McLaren12345/EFIS/Images/IMG_1576.JPG

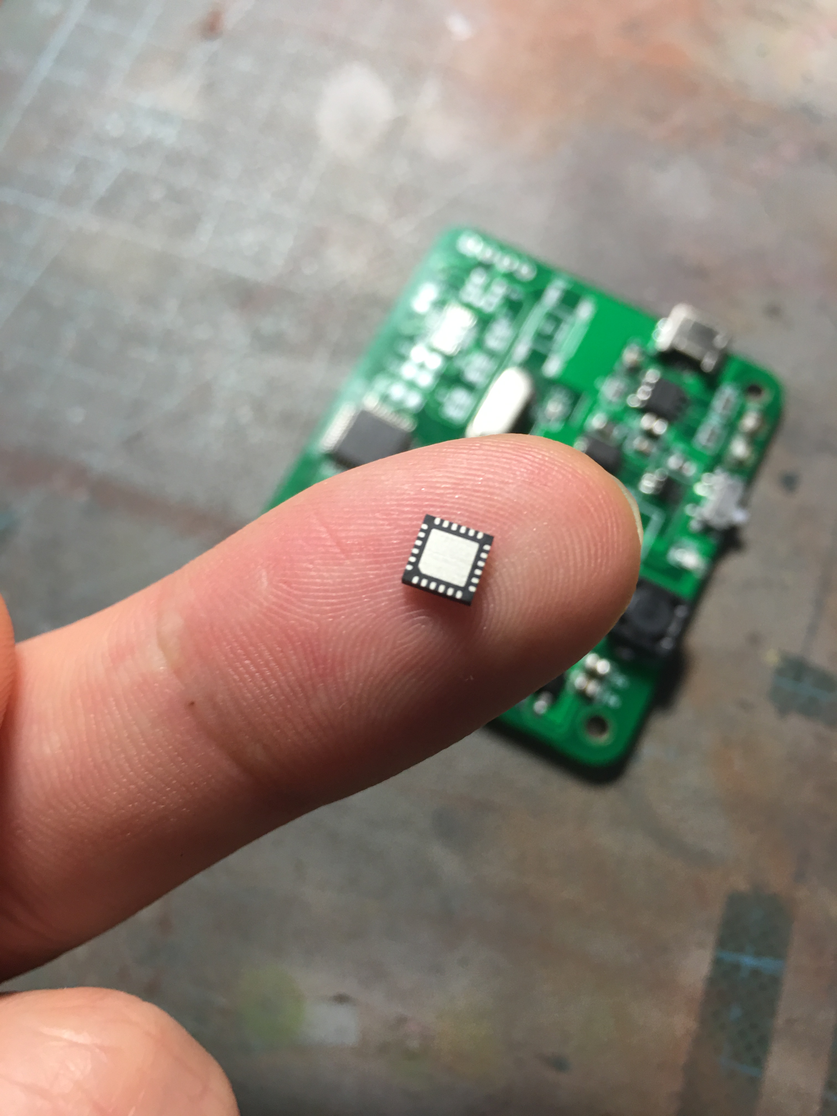
Images/IMG_1576.JPG
