McLaren12345/EFIS/Images/IMG_1605.JPG

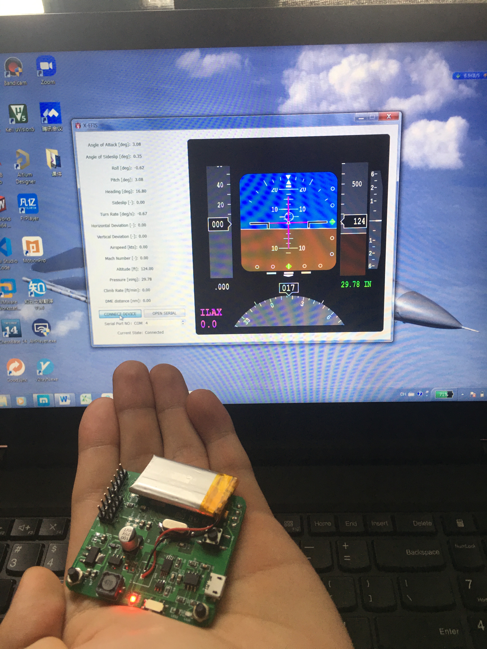
Images/IMG_1605.JPG
