McLaren12345/EFIS/Images/IMG_1611.JPG

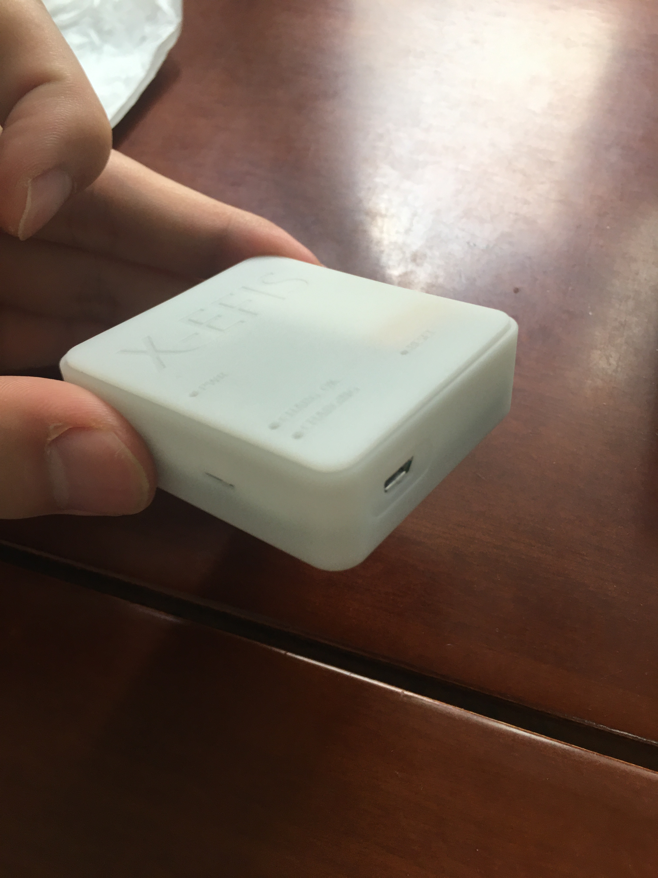
Images/IMG_1611.JPG
