McLaren12345/EFIS/Images/IMG_1615.JPG

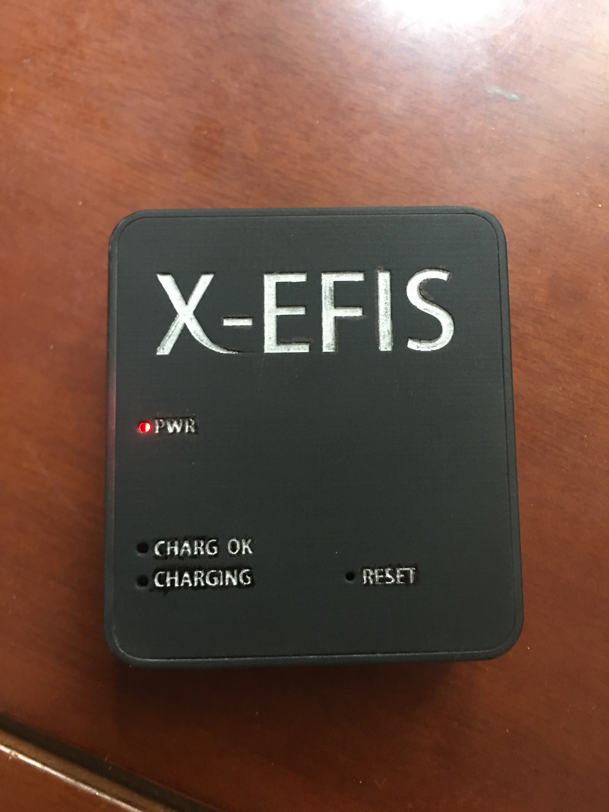
Images/IMG_1615.JPG
